raypp2/luma/moodBoardAssets/acrylic-front.png

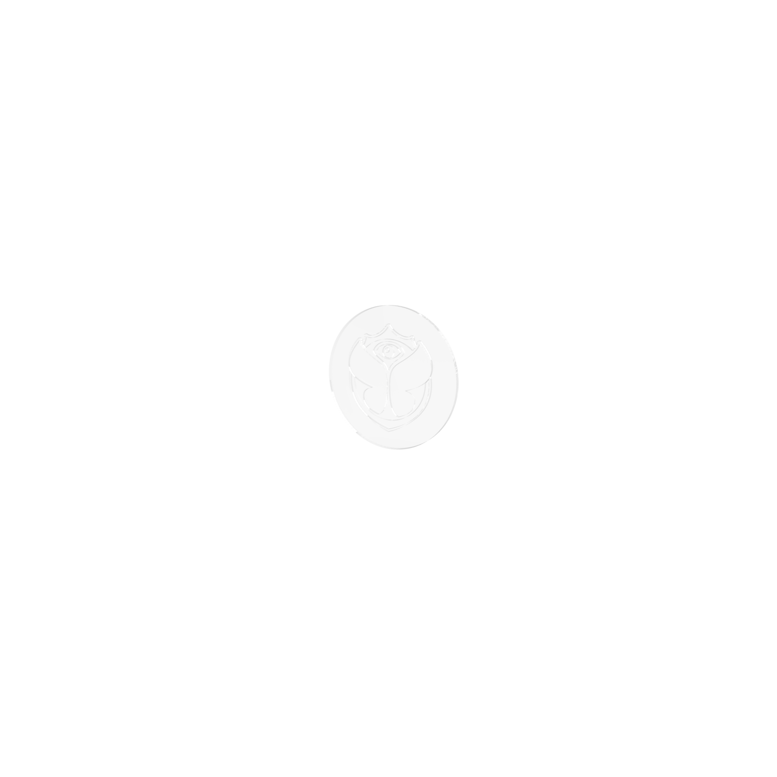
moodBoardAssets/acrylic-front.png
