raypp2/luma/moodBoardAssets/pcb-back.png

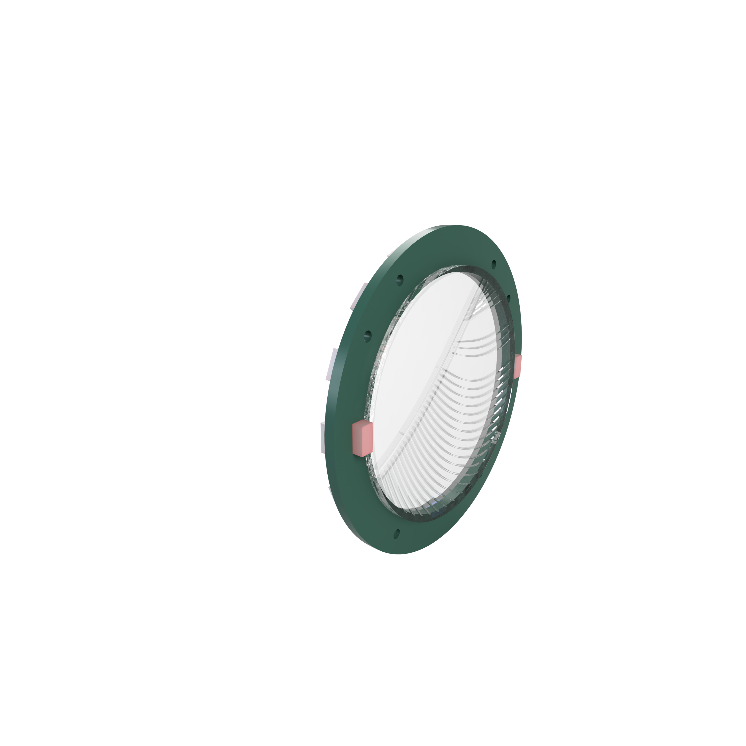
moodBoardAssets/pcb-back.png
