raypp2/luma/moodBoardAssets/pcb-render.png

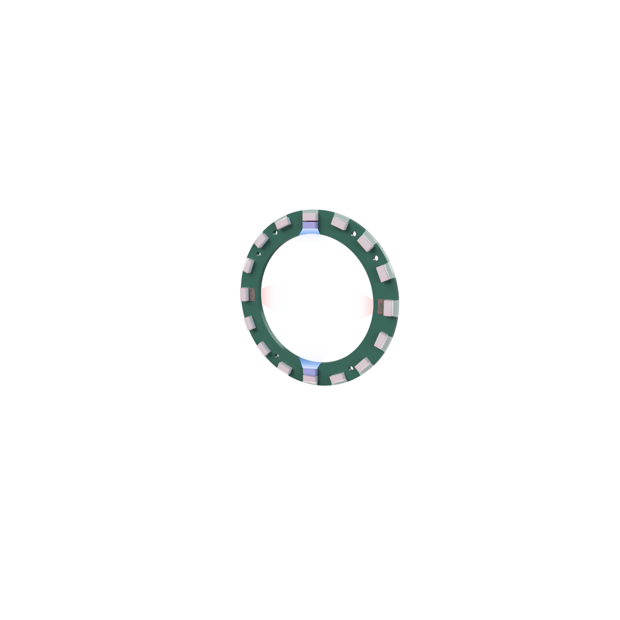
moodBoardAssets/pcb-render.png
